prezeskk/pcb-ks0108-128x64-glcd/output/PCB-Back.png

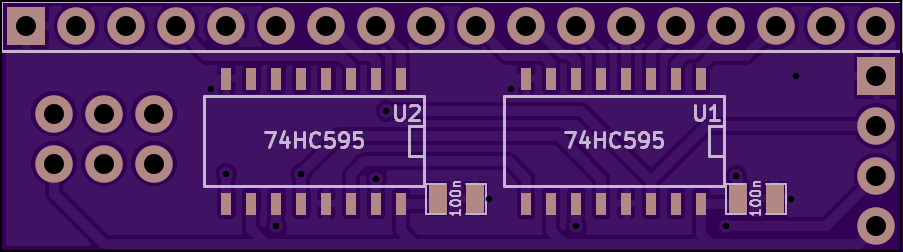
output/PCB-Back.png
