prezeskk/pcb-ks0108-128x64-glcd/output/PCB-Front.png

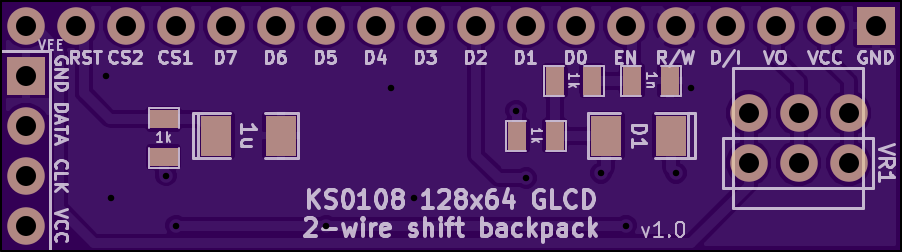
output/PCB-Front.png
