prezeskk/pcb-ks0108-128x64-glcd/output/Schematic.png

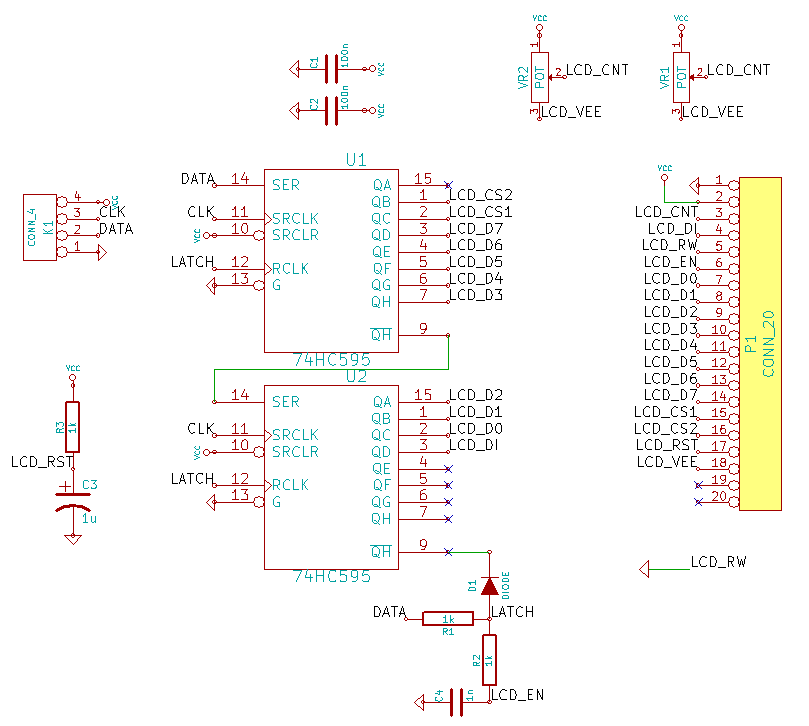
output/Schematic.png
